SYSC3010-W24/sysc3010-project-l1-g8/WeeklyUpdates/Week6/Saja_Fawagreh_week6.md

## Weekly Individual Project Update Report

### Group number: L1-G8

### Student name: Saja Fawagreh

### Week: 6 (14 Feb - 27 Feb)

---

1. **How many hours did you spend on the project this week? (0-10)**

2 hours

2. **Give a rough breakdown of hours spent on 1-3 of the following:\***
   (meetings, information gathering, design, research, brainstorming, evaluating options, prototyping options, writing/documenting, refactoring, testing, software implementation, hardware implementation)

   1. Researching sample code for local network communication protocols (2 hour)

3. **_What did you accomplish this week?_** _(Be specific)_

- Finalized component list for the component request form
- Determined how to establish and manage communication between devices on the local network

4. **_How do you feel about your progress?_** _(brief, free-form reflection)_

- I'm satisfied with our progress, but eager to commence work on FANS soon.

5. **_What are you planning to do next week_**? _(give specific goals)_

- Writing sample code for implementing communication between devices on the local network
- Begin experimenting with data transmission and reception between devices on the local network

6. **_Is anything blocking you that you need from others?_** _(What do you need from whom)_

- No
