SYSC3010-W24/sysc3010-project-l1-g8/WeeklyUpdates/Week5/Matteo_Golin_week5.md

## Weekly Individual Project Update Report

### Group number: L1-G8

### Student name: Matteo Golin

### Week: 5 (7 Feb - 13 Feb)

---

1. **How many hours did you spend on the project this week? (0-10)**

I spent 8.5 hours this week.

2. **Give rough breakdown of hours spent on 1-3 of the following:\***
   (meetings, information gathering, design, research, brainstorming, evaluating options, prototyping options, writing/documenting, refactoring, testing, software implementation, hardware implementation)

   1. Meeting with team members to discuss the final project proposal: 1.5 hours
   2. Reviewing peer feedback: 1 hour
   3. Writing the system design of the project proposal and creating sequence diagrams: 5 hours
   4. Porting project proposal to LaTeX: 1 hour

3. **_What did you accomplish this week?_** _(Be specific)_

- Finished the final proposal.
- Worked out any rough patches of the design idea among the team
- Divided up tasks to begin work over reading week
- Explored alternative hardware for the wearable Pi Pico

4. **_How do you feel about your progress?_** _(brief, free-form reflection)_

- I'm very glad the proposal is complete, because it took a lot of time to finish.
  - I'm feeling better about the project timeline now that it's be thought about and finalized in our proposal; it
    seems that we have a clearer idea of what to do now.

5. **_What are you planning to do next week_**? _(give specific goals)_

- Set up Firebase real-time DB for our project
- Start reading and posting temperature sensor data to the DB

6. **_Is anything blocking you that you need from others?_** _(What do you need from whom)_

- I would also need the smoke detecting sensor to complete my sensor tasks, but we have to purchase/acquire it from
  Carleton first.
