SYSC3010-W24/sysc3010-project-l1-g8/docs/final-report/final-report.tex

\documentclass[11pt]{article}
\usepackage[letterpaper, margin=1in]{geometry}
\usepackage{enumitem}

% Proper links
\usepackage[
    pdftitle={SYSC3010 Computer Systems Development Project - FANS Final Report},
    colorlinks=false,
    allbordercolors={0 0 0},
    citebordercolor={1 1 1}, % No border for citations
    pdfborderstyle={/S/U/W 1},
]{hyperref}

% Display graphics nicely
\usepackage{float}
\usepackage{graphicx}

\def\imagewidth{4in}

% Display JSON nicely
\usepackage{listings}
\usepackage{xcolor}

\colorlet{punct}{red!60!black}
\definecolor{background}{HTML}{EEEEEE}
\definecolor{delim}{RGB}{20,105,176}
\colorlet{numb}{magenta!60!black}
\lstdefinelanguage{json}{
    basicstyle=\normalfont\ttfamily,
    numbers=left,
    numberstyle=\scriptsize,
    stepnumber=1,
    numbersep=8pt,
    showstringspaces=false,
    breaklines=true,
    frame=lines,
    backgroundcolor=\color{background},
    literate=
     *{0}{{{\color{numb}0}}}{1}
      {1}{{{\color{numb}1}}}{1}
      {2}{{{\color{numb}2}}}{1}
      {3}{{{\color{numb}3}}}{1}
      {4}{{{\color{numb}4}}}{1}
      {5}{{{\color{numb}5}}}{1}
      {6}{{{\color{numb}6}}}{1}
      {7}{{{\color{numb}7}}}{1}
      {8}{{{\color{numb}8}}}{1}
      {9}{{{\color{numb}9}}}{1}
      {:}{{{\color{punct}{:}}}}{1}
      {,}{{{\color{punct}{,}}}}{1}
      {\{}{{{\color{delim}{\{}}}}{1}
      {\}}{{{\color{delim}{\}}}}}{1}
      {[}{{{\color{delim}{[}}}}{1}
      {]}{{{\color{delim}{]}}}}{1},
}

% References
\usepackage[style=ieee]{biblatex}
\addbibresource{./references.bib}

% Remove paragraph indentation and use newline to separate instead. %
\usepackage[parfill]{parskip}
\setlength{\parindent}{0cm}

\author{
    Grant Achuzia, 101222695 \\
    Javeria Sohail, 101197163 \\
    Matteo Golin, 101220709 \\
    Saja Fawagreh, 101217326 \\
    TA: Sean Kirkby
}
\title{
    SYSC3010 Computer Systems Development Project \\
    FANS Final Report \\
    {\large Group L1-G8} \\
    {
        \vspace{0.5in}
        \centering
         \\
        \small \url{https://github.com/SYSC3010-W24/sysc3010-project-l1-g8}
    }

}
\date{
    Created: April 3rd, 2024 \\
    Modified: \today
}

\begin{document}

% TITLE %
\maketitle
\pagenumbering{gobble} % Don't number title page
\pagebreak

% TABLE OF CONTENTS %
\pagenumbering{arabic} % Start numbering again
{
    \hypersetup{hidelinks}
    \tableofcontents
}
\pagebreak

% MAIN MATTER %
\input{sections/introduction}
\input{sections/final-solution}
\input{sections/discussion}
\input{sections/contributions}
\input{sections/reflections}

% BIBLIOGRAPHY %
\pagebreak
\printbibliography

% APPENDIX %
\input{sections/appendix}

\end{document}
