SYSC3010-W24/sysc3010-project-l1-g8/docs/design-report/design-report.tex

\documentclass[11pt]{article}
\usepackage[letterpaper, margin=1in]{geometry}

% Proper links
\usepackage[
    pdftitle={SYSC3010 Computer Systems Development Project - FANS Project Proposal},
    colorlinks=false,
    allbordercolors={0 0 0},
    citebordercolor={1 1 1}, % No border for citations
    pdfborderstyle={/S/U/W 1},
]{hyperref}

% Display graphics nicely
\usepackage{float}
\usepackage{graphicx}

% Display JSON nicely
\usepackage{listings}
\usepackage{xcolor}

\colorlet{punct}{red!60!black}
\definecolor{background}{HTML}{EEEEEE}
\definecolor{delim}{RGB}{20,105,176}
\colorlet{numb}{magenta!60!black}
\lstdefinelanguage{json}{
    basicstyle=\normalfont\ttfamily,
    numbers=left,
    numberstyle=\scriptsize,
    stepnumber=1,
    numbersep=8pt,
    showstringspaces=false,
    breaklines=true,
    frame=lines,
    backgroundcolor=\color{background},
    literate=
     *{0}{{{\color{numb}0}}}{1}
      {1}{{{\color{numb}1}}}{1}
      {2}{{{\color{numb}2}}}{1}
      {3}{{{\color{numb}3}}}{1}
      {4}{{{\color{numb}4}}}{1}
      {5}{{{\color{numb}5}}}{1}
      {6}{{{\color{numb}6}}}{1}
      {7}{{{\color{numb}7}}}{1}
      {8}{{{\color{numb}8}}}{1}
      {9}{{{\color{numb}9}}}{1}
      {:}{{{\color{punct}{:}}}}{1}
      {,}{{{\color{punct}{,}}}}{1}
      {\{}{{{\color{delim}{\{}}}}{1}
      {\}}{{{\color{delim}{\}}}}}{1}
      {[}{{{\color{delim}{[}}}}{1}
      {]}{{{\color{delim}{]}}}}{1},
}

% References
\usepackage[style=ieee]{biblatex}
\addbibresource{./references.bib}

% Remove paragraph indentation and use newline to separate instead. %
\usepackage[parfill]{parskip}
\setlength{\parindent}{0cm}

\author{
    Grant Achuzia, 101222695 \\
    Javeria Sohail, 101197163 \\
    Matteo Golin, 101220709 \\
    Saja Fawagreh, 101217326 \\
    TA: Sean Kirkby
}
\title{
    SYSC3010 Computer Systems Development Project \\
    FANS Detailed Design Report \\
    {\large Group L1-G8} \\
    {
        \vspace{0.5in}
        \centering
         \\
        \small \cite{header-img}
    }
}
\date{
    Created: March 11th, 2024 \\
    Modified: \today
}

\begin{document}

% TITLE %
\maketitle
\pagebreak

% TABLE OF CONTENTS %
{
    \hypersetup{hidelinks}
    \tableofcontents
}

% MAIN MATTER %
\include{sections/introduction}
\include{sections/design}
\include{sections/software}
\include{sections/hardware}
\include{sections/gui}
\include{sections/testing}
\include{sections/project}

% BIBLIOGRAPHY %
\pagebreak
\printbibliography

\end{document}
