SYSC3010-W24/sysc3010-project-l1-g8/docs/proposal/proposal.tex

\documentclass[11pt]{article}
\usepackage[letterpaper, margin=1in]{geometry}

% Proper links
\usepackage[
    pdftitle={SYSC3010 Computer Systems Development Project - FANS Project Proposal},
    colorlinks=false,
    allbordercolors={0 0 0},
    citebordercolor={1 1 1}, % No border for citations
    pdfborderstyle={/S/U/W 1},
]{hyperref}

% Display graphics nicely
\usepackage{float}
\usepackage{graphicx}

% References
\usepackage[style=ieee]{biblatex}
\addbibresource{./references.bib}

% Remove paragraph indentation and use newline to separate instead. %
\usepackage[parfill]{parskip}
\setlength{\parindent}{0cm}

\author{
    Grant Achuzia, 101222695 \\
    Javeria Sohail, 101197163 \\
    Matteo Golin, 101220709 \\
    Saja Fawagreh, 101217326 \\
    TA: Sean Kirkby
}
\title{
    SYSC3010 Computer Systems Development Project \\
    FANS Project Proposal \\
    {\large Group L1-G8} \\
    {
        \vspace{0.5in}
        \centering
         \\
        \small \cite{header-img}
    }
}
\date{
    Created: February 11th, 2024 \\
    Modified: \today
}

\begin{document}

% TITLE %
\maketitle
\pagebreak

% TABLE OF CONTENTS %
{
    \hypersetup{hidelinks}
    \tableofcontents
}

% MAIN MATTER %
\include{sections/introduction}
\include{sections/system-design}
\include{sections/work-plan}
\include{sections/project-requirements}
\include{sections/additional-hw}

% BIBLIOGRAPHY %
\pagebreak
\printbibliography

\end{document}
