SYSC3010-W24/sysc3010-project-l1-g8/docs/final-report/sections/contributions.tex

\section{Contributions}

This section lists all of the contributions of each member on the FANS development team.

\subsection{Code Contributions}

Code file contributions listed in this table will use Unix file paths to describe which files were worked on by each
contributor. The asterisk signifies the wildcard operator, so \texttt{alarm-system/*} captures all files within the
alarm-system/ directory. All paths correspond to paths within the project repository on GitHub.

For a more granular view of contributions for files with multiple authors, please review the Git commit history.

\begin{table}[H]
    \centering
    \footnotesize
    \begin{tabular}{| c | p{5in} |}
        \hline
        Author         & Code files                                                                 \\
        \hline
        Grant Achuzia  &
        \texttt{docs/*}, \texttt{web-app/*}, \texttt{pico\_alarm/*}, \texttt{README.md}             \\
        \hline
        Saja Fawagreh  &
        \texttt{docs/*}, \texttt{notifier/*}, \texttt{notifier/tests/test\_email\_notification\_system.py},
        \texttt{README.md}                                                                          \\
        \hline
        Javeria Sohail &
        \texttt{docs/*}, \texttt{pico\_alarm/*}, \texttt{haptic\_alarm\_test/*}, \texttt{README.md} \\
        \hline
        Matteo Golin   &
        \texttt{alarm-system/*}, \texttt{sensor-pi/*}, \texttt{web-app/main.py},
        \texttt{web-app/templates/index.html}, \texttt{web-app/templates/settings.html}, \texttt{docs/*},
        \texttt{notifier/templates/*}, \texttt{notifier/tests/test\_email.py}, \texttt{notifier/messages.py},
        \texttt{README.md}                                                                          \\
        \hline
    \end{tabular}
    \caption{The individual code contributions of each FANS team member.}
\end{table}

\subsection{Report Contributions}

\begin{table}[H]
    \centering
    \footnotesize
    \begin{tabular}{| c | p{5in} |}
        \hline
        Author         & Report sections                                                                      \\
        \hline
        Grant Achuzia  & Project Success, Learning Experiences, Appendix A                                    \\
        \hline
        Saja Fawagreh  & Message Protocols, Sequence Diagrams, Discussion, Appendix B                         \\
        \hline
        Javeria Sohail & Motivation, Problem Statement, Final Design Solution, Appendix B                     \\
        \hline
        Matteo Golin   & Contributions, Deployment Diagram, Project Extensions, Sequence Diagrams, Discussion \\
        \hline
    \end{tabular}
    \caption{The individual final report contributions of each FANS team member.}
\end{table}
