SYSC3010-W24/sysc3010-project-l1-g8/docs/proposal/sections/additional-hw.tex

\section{Additional Hardware Required}

Developing FANS requires additional hardware that is described in the following tables. Table \ref{t:cu-hw} lists
hardware that is already provided by Carleton University, while Table \ref{t:extra-hw} shows any additional components
that will need to be purchased by the team.

\begin{table}[H]
    \centering
    \begin{tabular}{| c | c | c |}
        \hline
        Component       & Amount        & Digi-Key Number \\
        \hline
        Wires           & 50-100 pieces & N/A             \\
        \hline
        SenseHat Module & 4             & N/A             \\
        \hline
        Breadboard      & 4             & N/A             \\
        \hline
    \end{tabular}
    \caption{Additional hardware provided by Carleton University.}
    \label{t:cu-hw}
\end{table}

\begin{table}[H]
    \centering
    \begin{tabular}{| c | c | c |}
        \hline
        Component           & Amount & Digi-Key Number \\
        \hline
        AudioHat Module     & 1      & N/A             \\
        \hline
        Smoke Sensor        & 1      & 333102          \\
        \hline
        16x4 LCD Display    & 2      & EA DOGS164W-A   \\
        \hline
        Raspberry Pi Zero W & 1      & SC0065          \\
        \hline
    \end{tabular}
    \caption{Additional hardware to be bought by the team.}
    \label{t:extra-hw}
\end{table}
