SYSC3010-W24/sysc3010-project-l1-g8/WeeklyUpdates/Week11/Saja_Fawagreh_week11.md

## Weekly Individual Project Update Report

### Group number: L1-G8

### Student name: Saja Fawagreh

### Week: 11 (20 Mar - 26 Mar)

---

1. **How many hours did you spend on the project this week? (0-10)**

I spent 14 hours on the project this week.

2. **Give rough breakdown of hours spent on 1-3 of the following:\***
   (meetings, information gathering, design, research, brainstorming, evaluating options, prototyping options, writing/documenting, refactoring, testing, software implementation, hardware implementation)

   1. Completed the implementation of the Notification System (4 hours)
   2. Worked on the draft final report (2 hour)
   3. Filmed final demo video with group members and on my own (4 hours)
   4. Added my updated PEP8 code on Github (2 hour)
   5. Wrote installation instructions (2 hour)

3. **_What did you accomplish this week?_** _(Be specific)_

   - Completed the implementation of the Notification System on Raspberry Pico
   - Worked on the draft final report 
   - Filmed final demo video with group members and on my own
   - Made my code conform to PEP8
   - Wrote installation instructions
     
4. **_How do you feel about your progress?_** _(brief, free-form reflection)_

- I a very happy with the progress and that our project is almost done.

5. **_What are you planning to do next week_**? _(give specific goals)_

- Complete the term reflection
- Complete the final report
- Ensure that the code base conforms to proper standards and meets rubric expectations before submitting

6. **_Is anything blocking you that you need from others?_** _(What do you need from whom)_

- No
