SYSC3010-W24/sysc3010-project-l1-g8/WeeklyUpdates/Week11/Grant_Achuzia_week11.md

## Weekly Individual Project Update Report

### Group number: L1-G8

### Student name: Grant Achuzia

### Week: 11,  Wednesday March 27th 2024 - Tuesday April 2nd 2024

---

1. **How many hours did you spend on the project this week? (0-10)**

I spent 16 hours working on the project this week.

2. **Give rough breakdown of hours spent on 1-3 of the following:\***
   (meetings, information gathering, design, research, brainstorming, evaluating options, prototyping options, writing/documenting, refactoring, testing, software implementation, hardware implementation)

   1. Built circuit for the haptic alarm using the Pico W, 2 hours
   2. Implemented user authentication for the web application, 5 hours
   3. Recorded parts for final video, 4 hours
   3. Edited final video, 5 hours

3. **_What did you accomplish this week?_** _(Be specific)_

- I was able to get user authentication working, connecting the web application to the firebase database
- Recorded the final video with my group, and edited the final video for the  project
- Edited the final video for submission on Wednesday

4. **_How do you feel about your progress?_** _(brief, free-form reflection)_

- Good! Despite the heavy workload we were able to accomplish most of the tasks we set out to accomplish.

5. **_What are you planning to do next week_**? _(give specific goals)_

- Finish writing the Final Report

6. **_Is anything blocking you that you need from others?_** _(What do you need from whom)_

- None!
