SYSC3010-W24/sysc3010-project-l1-g8/WeeklyUpdates/Week9/Javeria_Sohail_Week9.md

## Weekly Individual Project Update Report

### Group number: L1-G8

### Student name: Javeria Sohail

### Week: 9 (13 Mar - 19 Mar)

---

1. **How many hours did you spend on the project this week? (0-10)**

I dedicated 8 hours to the project this week.

2. **Give rough breakdown of hours spent on 1-3 of the following:\***
   (meetings, information gathering, design, research, brainstorming, evaluating options, prototyping options, writing/documenting, refactoring, testing, software implementation, hardware implementation)

   1. Creating Unit Tests for the Haptic Alarm System: 3 hours
   2. Working on the Technical Memo: 5 hours

3. **_What did you accomplish this week?_** _(Be specific)_

- Decomposed the main script into functions to facilitate testing.
- Acquired knowledge on utilizing the Mock library for testing purposes.
- Authored unit tests for the Haptic alaram system.

4. **_How do you feel about your progress?_** _(brief, free-form reflection)_

- I'm very pleased with my progress this week, especially because we've nearly completed the project.

5. **_What are you planning to do next week_**? _(give specific goals)_

- I plan to focus on developing the pico and LED, aiming to finalize this critical component of our project.

6. **_Is anything blocking you that you need from others?_** _(What do you need from whom)_

- No
