SYSC3010-W24/sysc3010-project-l1-g8/WeeklyUpdates/Week9/Grant_Achuzia_week9.md

## Weekly Individual Project Update Report

### Group number: L1-G8

### Student name: Grant Achuzia

### Week: 9,  Wednesday March 13th 2024 - Tuesday March 19th 2024

---

1. **How many hours did you spend on the project this week? (0-10)**

I spent 10 hours working on the project this week.

2. **Give rough breakdown of hours spent on 1-3 of the following:\***
   (meetings, information gathering, design, research, brainstorming, evaluating options, prototyping options, writing/documenting, refactoring, testing, software implementation, hardware implementation)

   1. Implementing the new design for the web GUI, 6 hours
   2. Writing test cases for upcoming demo, 1 hour
   3. Trying to implement user authentication, 2 hours

3. **_What did you accomplish this week?_** _(Be specific)_

- I was able to implement the redesign the web GUI based on FBF feedback from last week
- Bought the ADC needed for the MQ2 sensor
- Wrote tests for the TA Unit Test Plan Demo
- Did research on user authentication for flask applications

4. **_How do you feel about your progress?_** _(brief, free-form reflection)_

- Slightly less anxious. We have all the components we need to begin building FANS, now we just need to find the time to build it.

5. **_What are you planning to do next week_**? _(give specific goals)_

- Add themes to the web UI
- Finish implementing web GUI, do user authentication with Flask
- See if I can help other team members with their parts

6. **_Is anything blocking you that you need from others?_** _(What do you need from whom)_

- None at the moment.
