SYSC3010-W24/sysc3010-project-l1-g8/docs/assets/sequence/EmergencyResponseUseCase.png

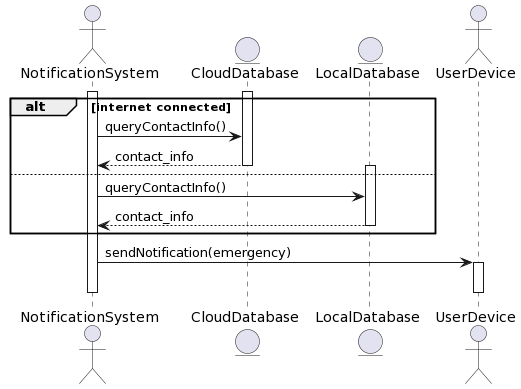
docs/assets/sequence/EmergencyResponseUseCase.png
