SYSC3010-W24/sysc3010-project-l1-g8/docs/assets/sequence/TriggerEmergencyUseCase.png

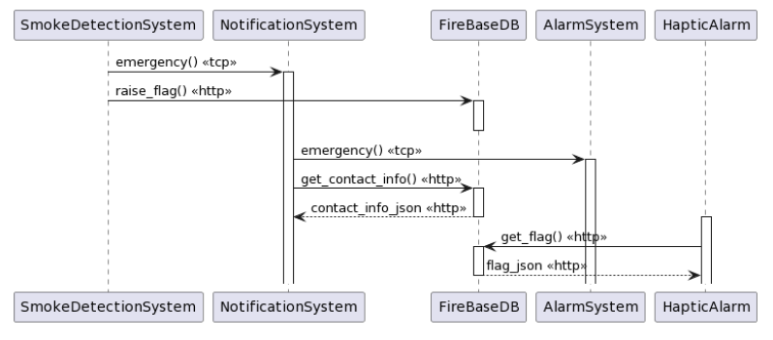
docs/assets/sequence/TriggerEmergencyUseCase.png
