SYSC3010-W24/sysc3010-project-l1-g8/alarm-system/messages.py

"""
This file defines the UDP messages which can be received over UDP. Each one
triggers an event in the state machine.
"""

from enum import IntEnum


class Messages(IntEnum):
    """
    Represents the types of messages that are possible to received over UDP.
    """

    EMERGENCY = 0
    EMERGENCY_OVER = 1
