SYSC3010-W24/sysc3010-project-l1-g8/alarm-system/tests/test_alarm.py

"""
This file tests that the buzzer connected to the Raspberry Pi behaves as
expected. This test must be run while the user can audibly verify that the
buzzer is sounding.
"""

from gpiozero import TonalBuzzer
from gpiozero.tones import Tone
import pytest
import time

# The GPIO pin on the Pi that the buzzer will need to be connected to
GPIO_PIN: int = 22

# The amount of time the buzzer will be on or off for during toggling
INTERVAL: float = 0.5


@pytest.fixture
def note() -> Tone:
    """The note for the buzzer to play."""
    return Tone.from_frequency(466.164)


@pytest.fixture
def buzzer() -> TonalBuzzer:
    """The note for the buzzer to play."""
    return TonalBuzzer(GPIO_PIN)


def test_buzzer_toggle(note: Tone, buzzer: TonalBuzzer) -> None:
    """Tests that the buzzer can be toggled on and off."""

    for _ in range(3):
        buzzer.play(note)
        time.sleep(INTERVAL)
        buzzer.stop()
        time.sleep(INTERVAL)
