SYSC3010-W24/sysc3010-project-l1-g8/alarm-system/tests/test_messages.py

"""
This file tests that messages can be parsed from plain integers.
"""

import pytest
from messages import Messages


def test_valid_messages() -> None:
    """
    Test that valid numerical values create their corresponding messages.
    """

    assert Messages(0) == Messages.EMERGENCY
    assert Messages(1) == Messages.EMERGENCY_OVER


def test_invalid_message() -> None:
    """
    Tests that numerical values outside the range of encoded messages cannot be
    decoded.
    """

    with pytest.raises(ValueError):
        Messages(2)
